sarthakchikte0312/MSPM0L1105_Dev_Board/images/1.png

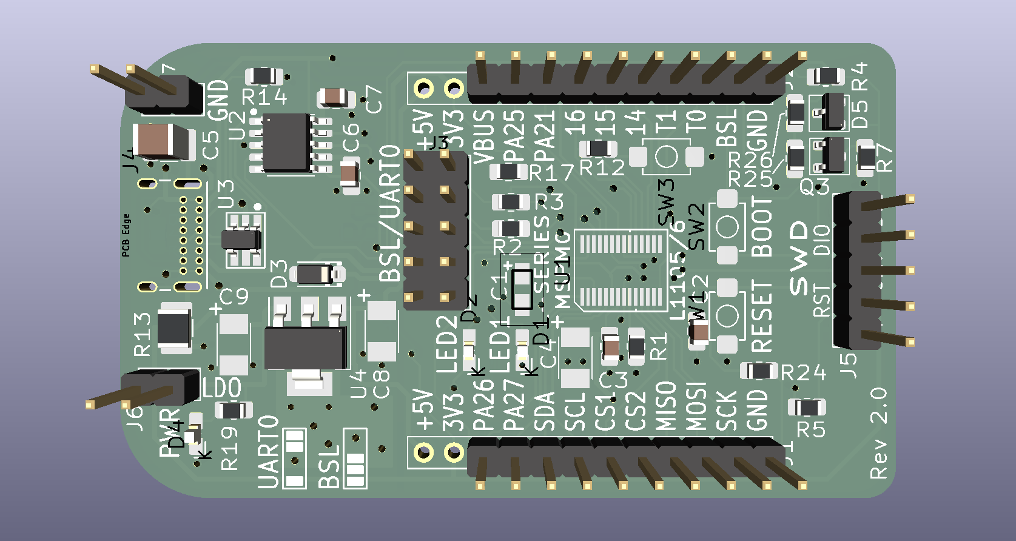
images/1.png
