sarthakchikte0312/MSPM0L1105_Dev_Board/images/2.png

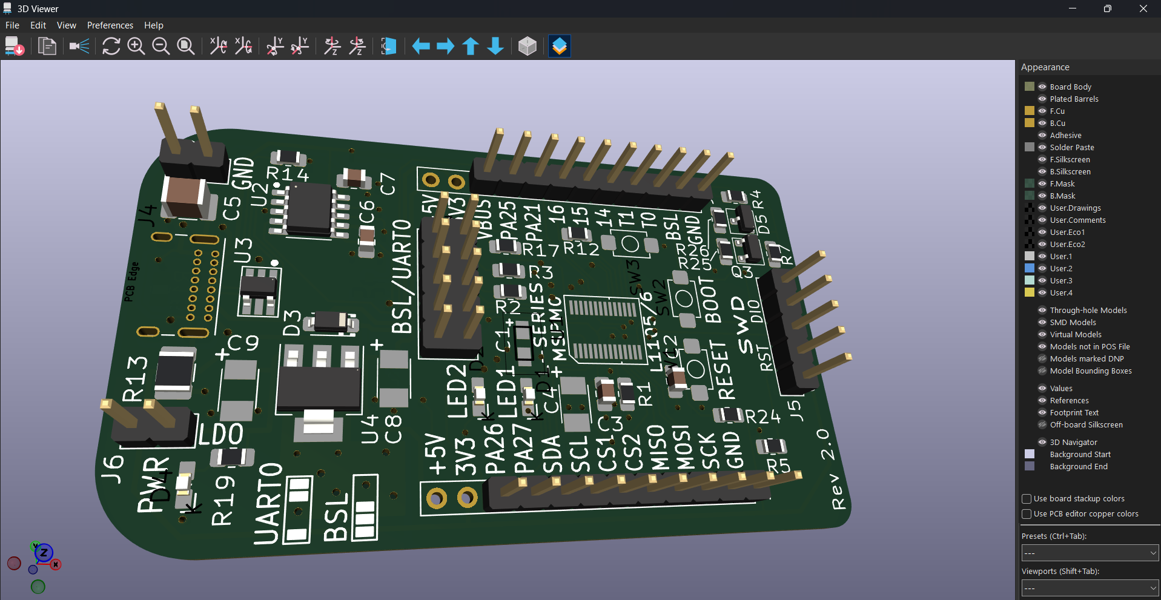
images/2.png
