sarthakchikte0312/MSPM0L1105_Dev_Board/images/3.png

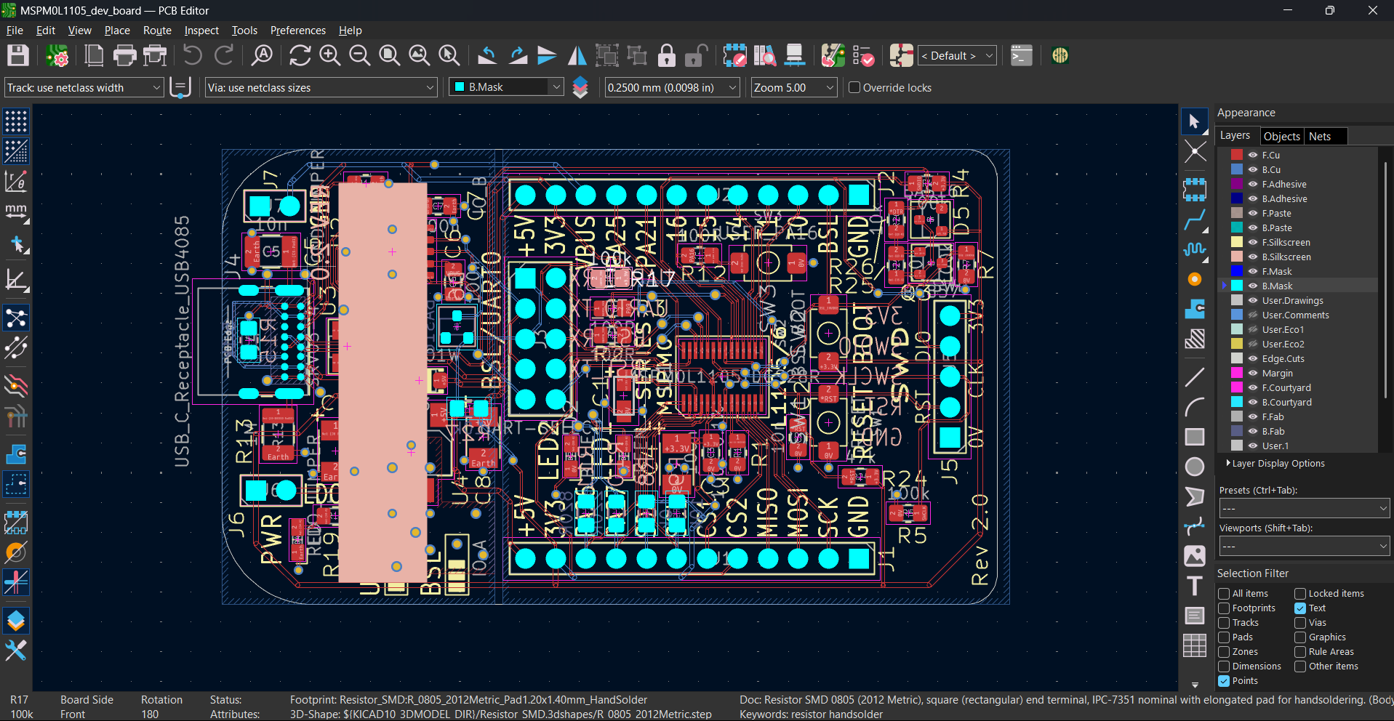
images/3.png
