sarthakchikte0312/MSPM0L1105_Dev_Board/images/4.png

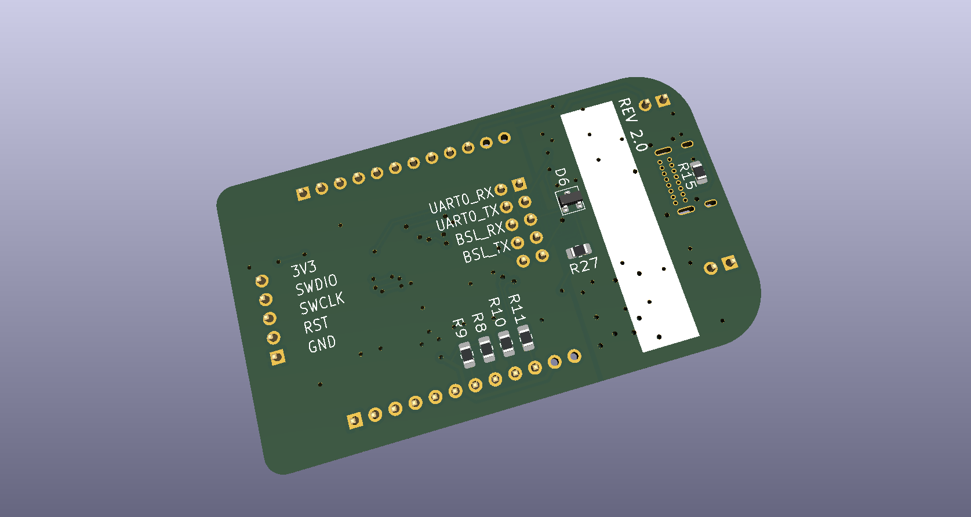
images/4.png
