sarthakchikte0312/MSPM0L1105_Dev_Board/images/5.png

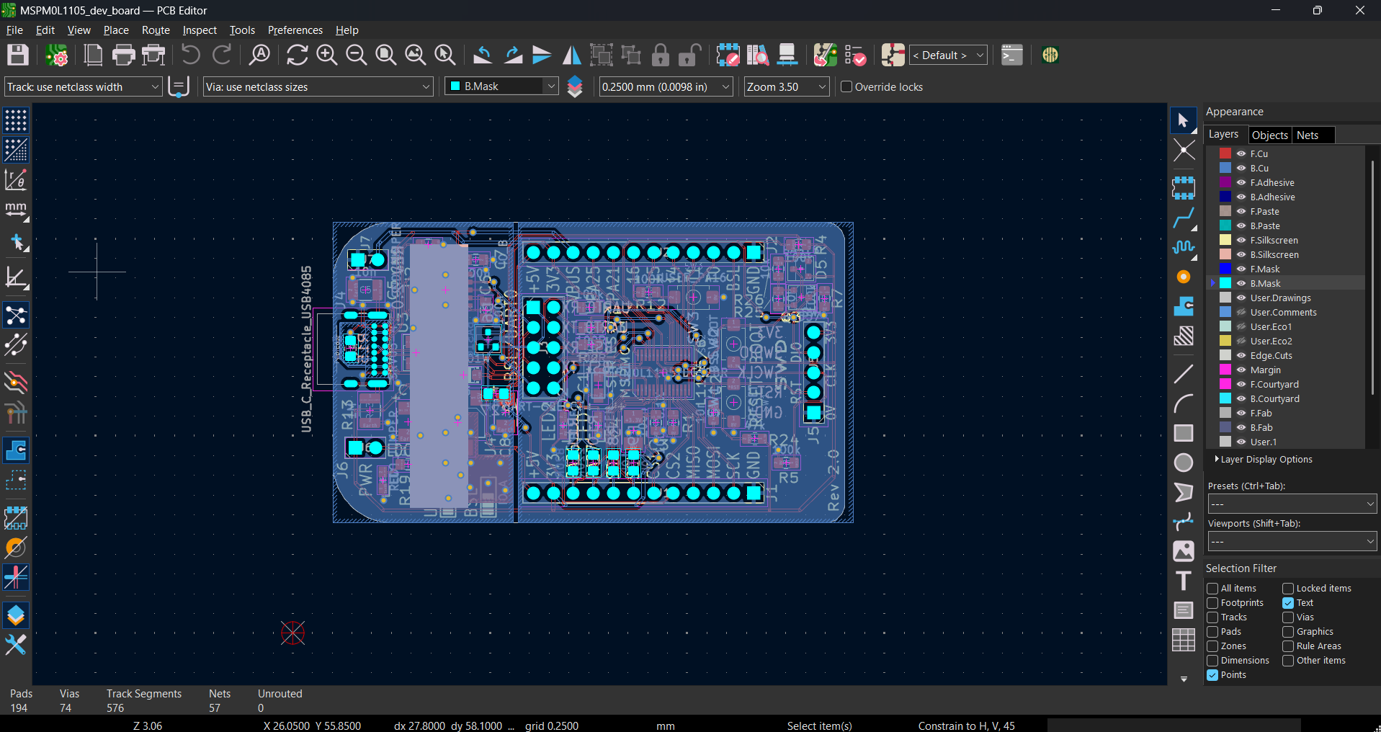
images/5.png
