sarthakchikte0312/MSPM0L1105_Dev_Board/images/6.png

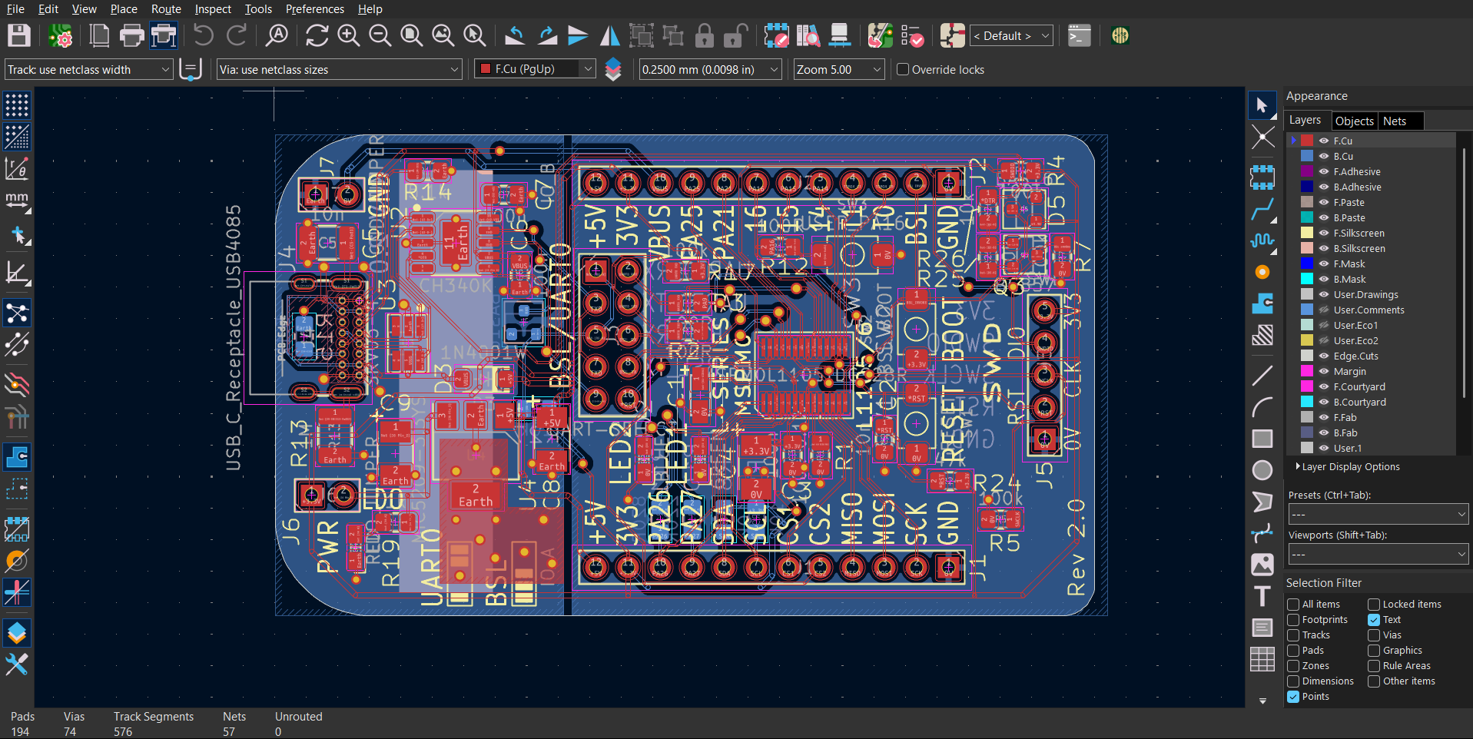
images/6.png
