sarthakchikte0312/MSPM0L1105_Dev_Board/images/7.png

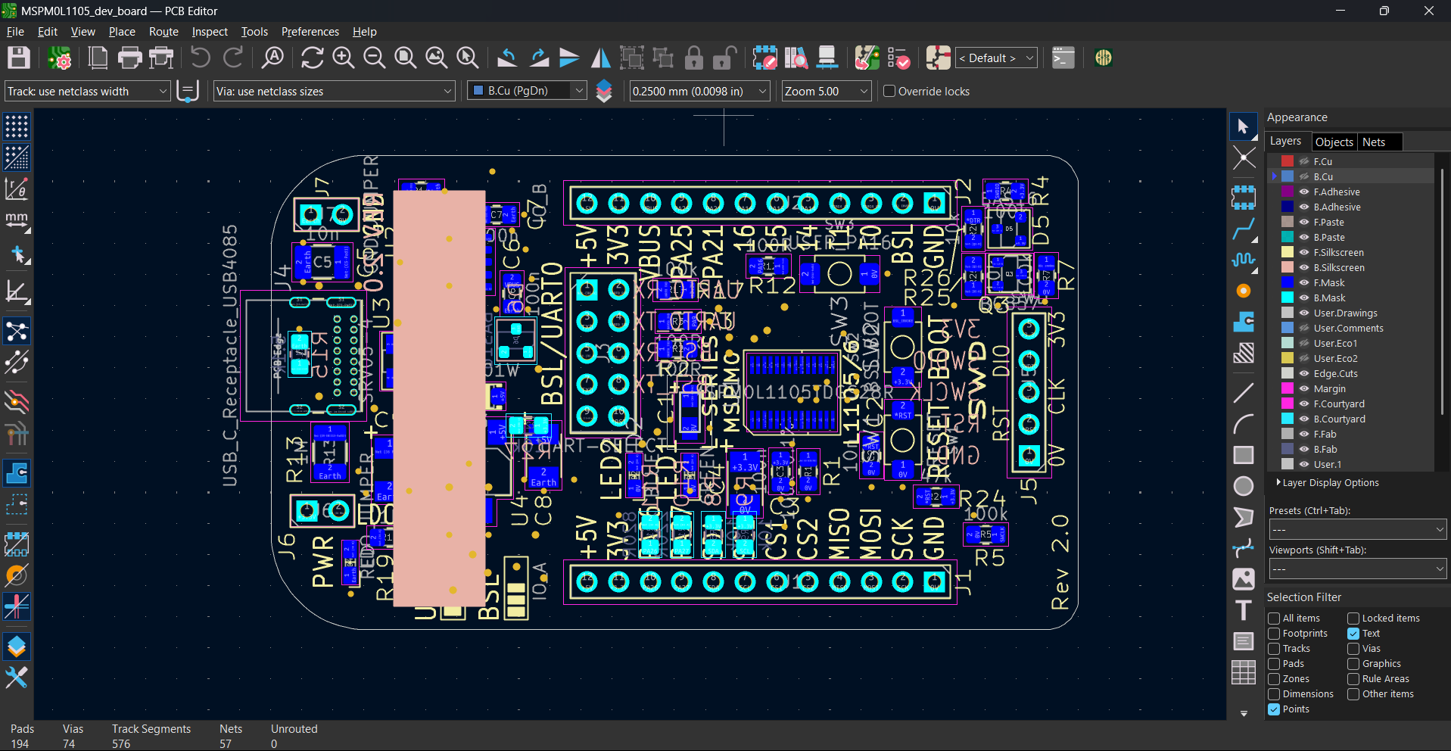
images/7.png
