sarthakchikte0312/MSPM0L1105_Dev_Board/images/8.png

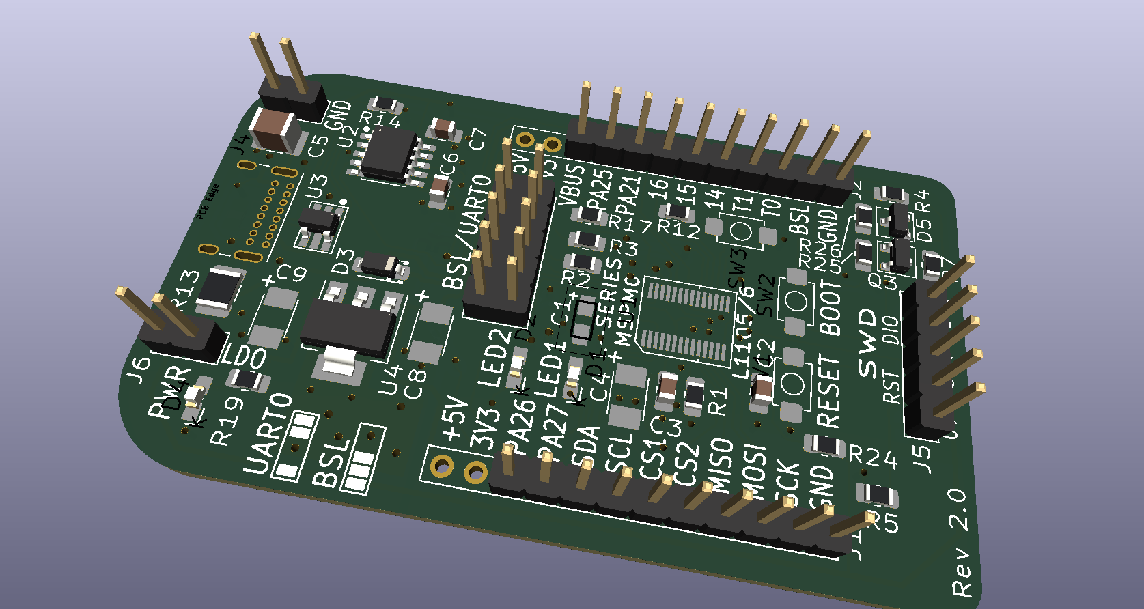
images/8.png
